michaelhayashi/ROV_Model_N/Rov_Basestation/ROV_BaseStation2012/rov.png

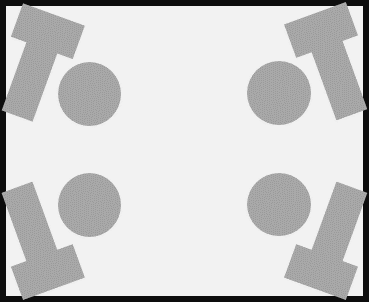
Rov_Basestation/ROV_BaseStation2012/rov.png
