michaelhayashi/ROV_Model_N/Rov_Basestation/ROV_BaseStation2012/ROV_Mission_Control/Top Down588.png

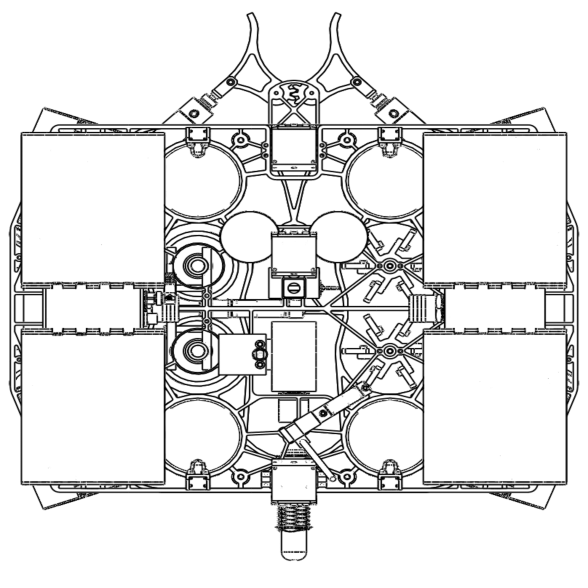
Rov_Basestation/ROV_BaseStation2012/ROV_Mission_Control/Top Down588.png
