michaelhayashi/ROV_Model_N/Rov_Basestation/rovgui.PNG

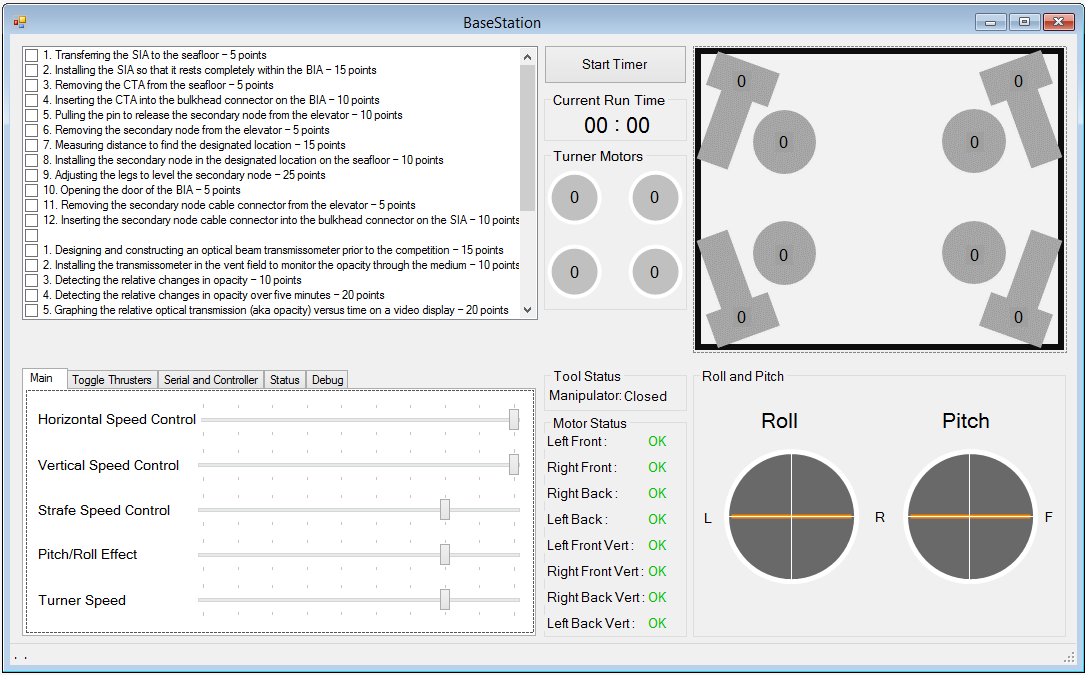
Rov_Basestation/rovgui.PNG
