michaelhayashi/ROV_Model_N/Rov_Basestation/XboxController.png

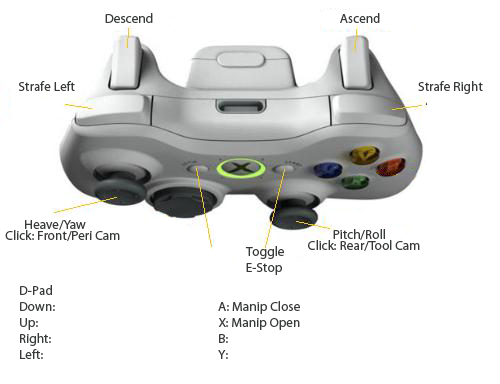
Rov_Basestation/XboxController.png
