michaelhayashi/ROV_Model_N/Rov_Basestation/ROV_BaseStation2012/ROV_Mission_Control/stdafx.cpp

// stdafx.cpp : source file that includes just the standard includes
// ROV_Mission_Control.pch will be the pre-compiled header
// stdafx.obj will contain the pre-compiled type information

#include "stdafx.h"
